maebemae/TheButton/The Buttoner/Core/Inc/user_interface.h

/*
 * usb_interface.h
 *
 *  Created on: Jan 11, 2025
 *      Author: mae
 */

#ifndef INC_USER_INTERFACE_H_
#define INC_USER_INTERFACE_H_

#include <stdio.h>
#include <stdbool.h>
#include <string.h>
#include "usb_app.h"
#include "user_menu.h"



#include "messages.h"
#include "user_data.h"



#endif /* INC_USER_INTERFACE_H_ */
