maebemae/TheButton/The Buttoner/Core/Inc/user_menu.h

/*
 * user_menu.h
 *
 *  Created on: Jan 11, 2025
 *      Author: mae
 */

#ifndef INC_USER_MENU_H_
#define INC_USER_MENU_H_


#define SIGNON0 "\r\nWelcome to The Button configurator\r\n\r\n\t1: to show current messages\r\n\t2: to edit messages\r\n\t9: to restore factory defaults\r\n\r\n"
#define ENTER_DFU "Entering DFU, bye bye\r\n"
#define MESSAGE_TOO_LONG "\r\nMessage too long\r\n"


#endif /* INC_USER_MENU_H_ */
